rwlloyd/stupid-solar-thing/md-assets/signal-2021-06-13-234058_002.jpeg

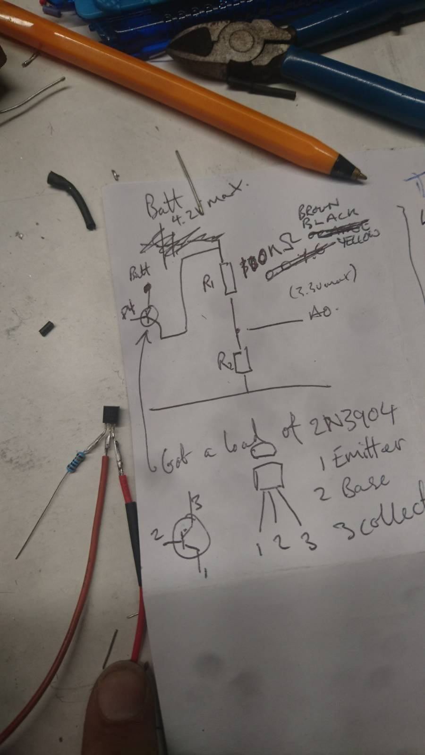
md-assets/signal-2021-06-13-234058_002.jpeg
