rwlloyd/stupid-solar-thing/md-assets/signal-2021-06-13-234058_003.jpeg

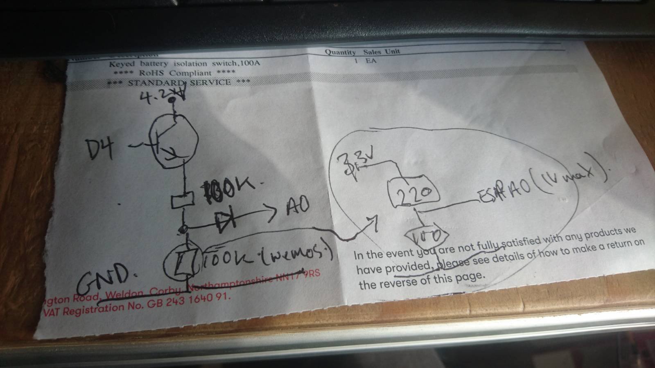
md-assets/signal-2021-06-13-234058_003.jpeg
