rwlloyd/stupid-solar-thing/md-assets/signal-2021-06-14-191512.jpeg

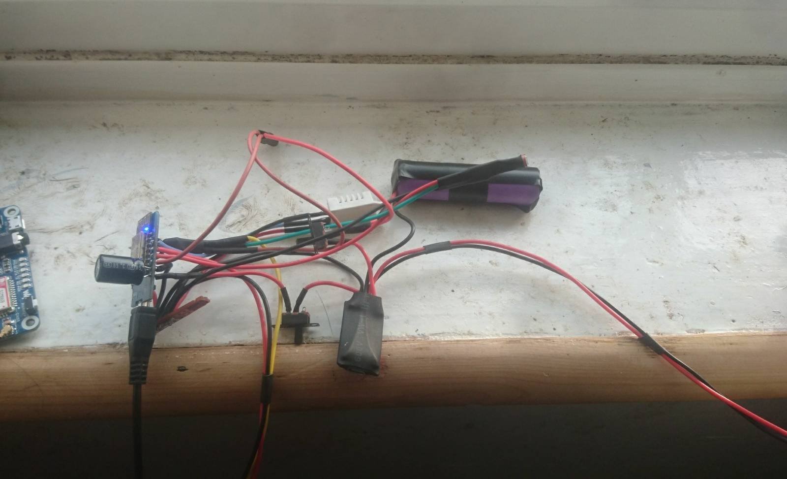
md-assets/signal-2021-06-14-191512.jpeg
