rwlloyd/stupid-solar-thing/inspiration/Wemos-CapMoistSen-test/Wemos-CapMoistSen-test.ino

const int AirValue = 1024;   //you need to replace this value with Value_1
const int WaterValue = 650;  //you need to replace this value with Value_2
const int SensorPin = A0;
int soilMoistureValue = 0;
int soilmoisturepercent = 0;

void setup() {
  Serial.begin(115200);
  // put your setup code here, to run once:

}

void loop() {
  // put your main code here, to run repeatedly:

  soilMoistureValue = analogRead(SensorPin);  //put Sensor insert into soil
  Serial.println(soilMoistureValue);
  delay(250);
}
